AndreasGerken/demoPuppy/packs/puppy_v05_one_part/one_part_body.stl

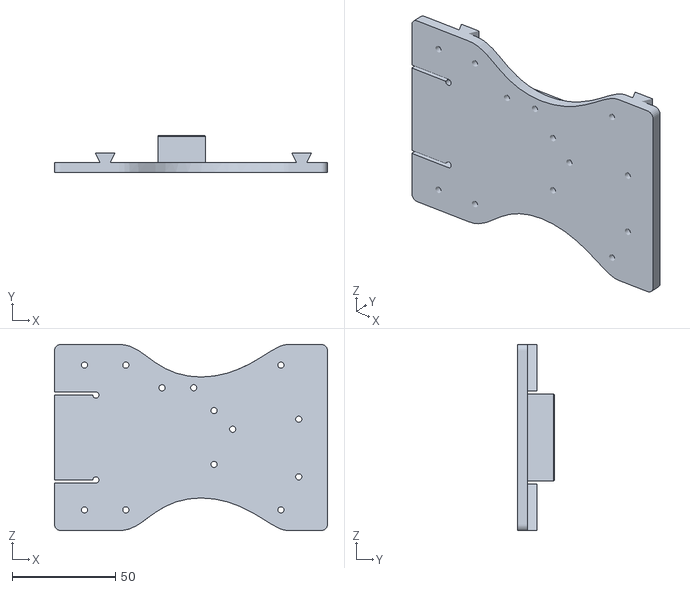
[picture p22: CAD file, 2017-08-01]
packs/puppy_v05_one_part/one_part_body.stl
132.0 x 18.0 x 90.0
