AndreasGerken/demoPuppy/models/servo_holder_HS-81/utility/HS-81MG_horn.SLDPRT

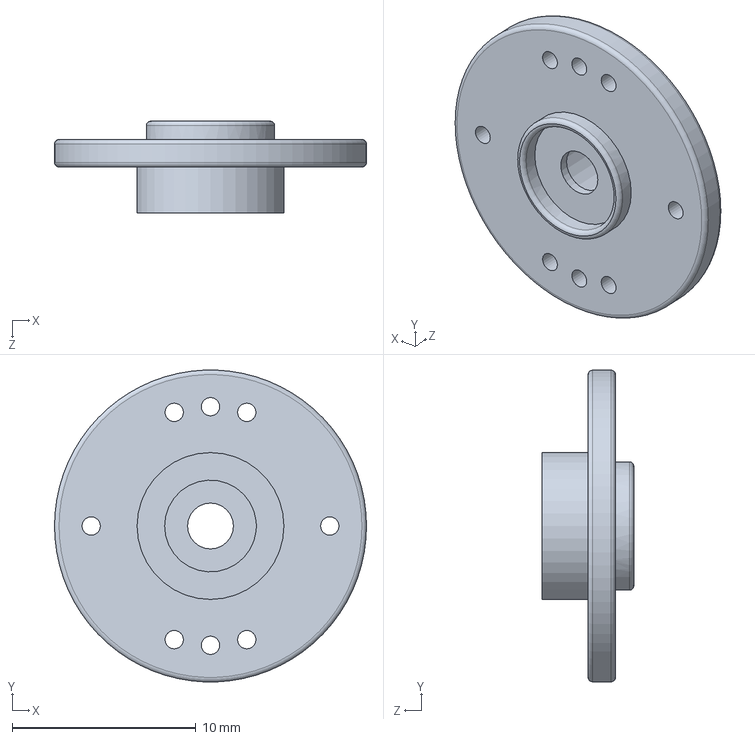
[picture p23: CAD file, 2017-07-04]
models/servo_holder_HS-81/utility/HS-81MG_horn.SLDPRT
17.0 x 17.0 x 5.00 mm
