AndreasGerken/demoPuppy/models/two_part_body/solidworks/holder_part.SLDPRT

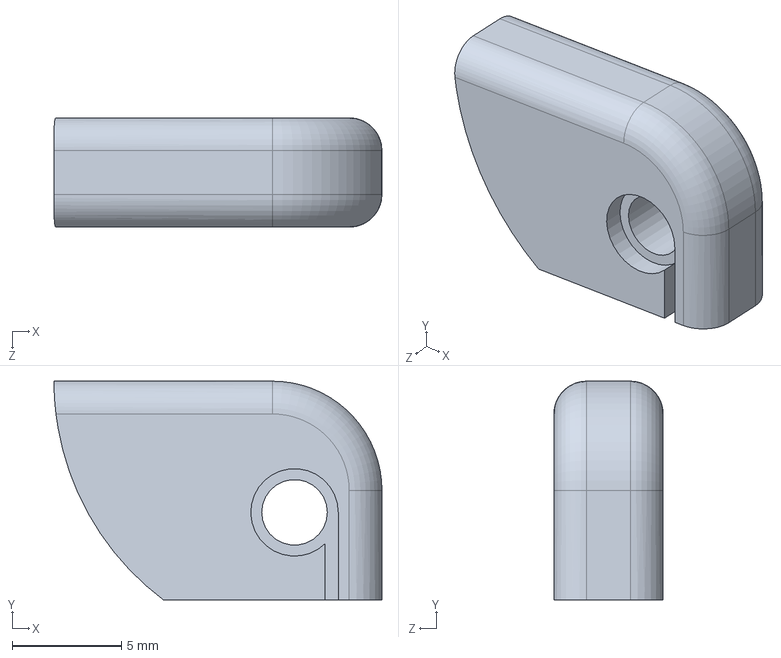
[picture p24: CAD file, 2017-07-04]
models/two_part_body/solidworks/holder_part.SLDPRT
15.0 x 10.0 x 5.00 mm
