AndreasGerken/demoPuppy/models/two_part_body/stl/puppy_v04_flexSpine - holder_part-1.STL

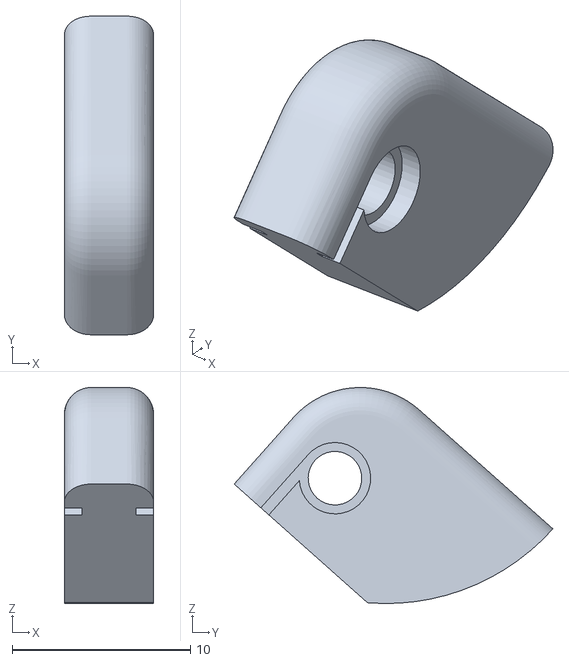
[picture p25: CAD file, 2017-07-04]
models/two_part_body/stl/puppy_v04_flexSpine - holder_part-1.STL
5.00 x 17.9 x 12.1
