AndreasGerken/demoPuppy/models/two_part_leg/solidworks/LowerLeg_v2_right.SLDPRT

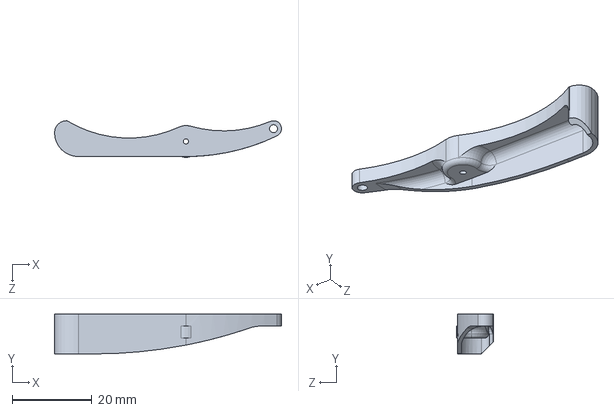
[picture p26: CAD file, 2017-07-04]
models/two_part_leg/solidworks/LowerLeg_v2_right.SLDPRT
57.0 x 10.0 x 9.18 mm
