AndreasGerken/demoPuppy/packs/puppy_v05_one_part/imu_MPU6050_holder.stl

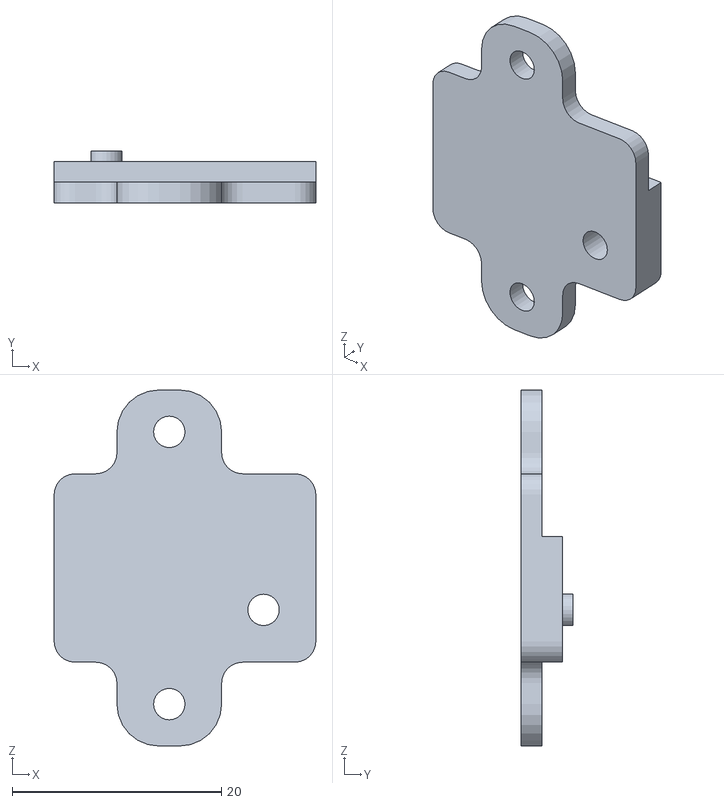
[picture p27: CAD file, 2017-07-04]
packs/puppy_v05_one_part/imu_MPU6050_holder.stl
25.0 x 5.00 x 34.0
