AndreasGerken/demoPuppy/models/two_part_body/solidworks/spine.SLDPRT

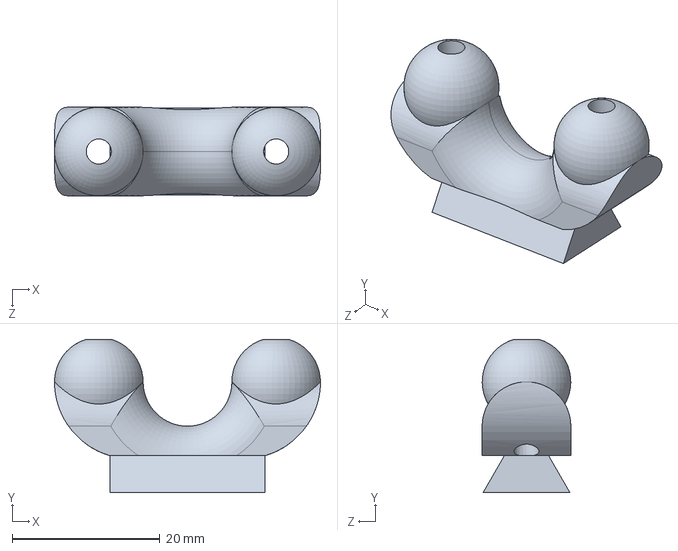
[picture p28: CAD file, 2017-07-04]
models/two_part_body/solidworks/spine.SLDPRT
36.0 x 20.8 x 12.0 mm
