AndreasGerken/demoPuppy/packs/puppy_v05_one_part/servo_holder_CS-3.stl

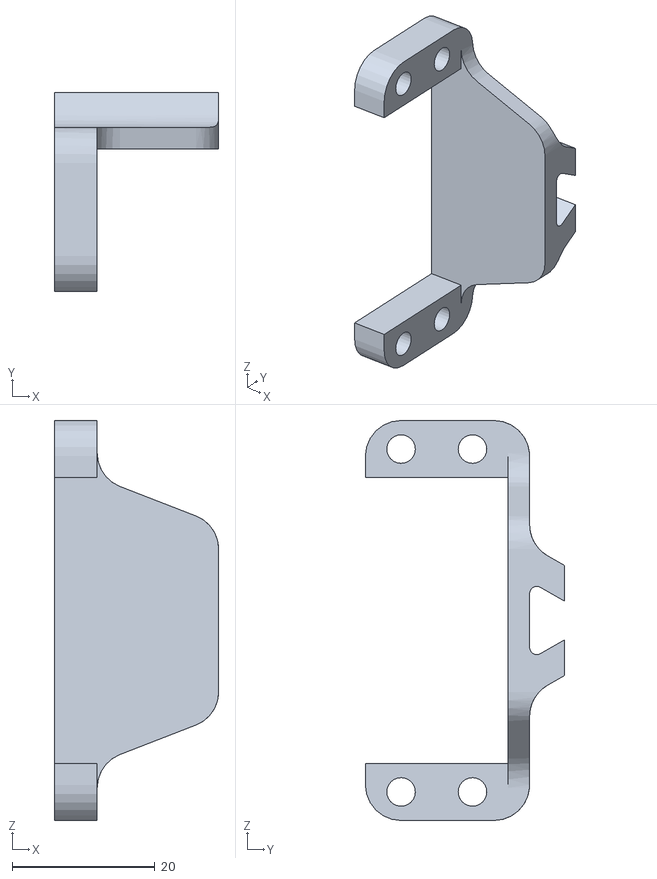
[picture p29: CAD file, 2017-07-04]
packs/puppy_v05_one_part/servo_holder_CS-3.stl
23.0 x 27.9 x 56.0
