AndreasGerken/demoPuppy/models/two_part_body/stl/puppy_v04_flexSpine - body_front-1.STL

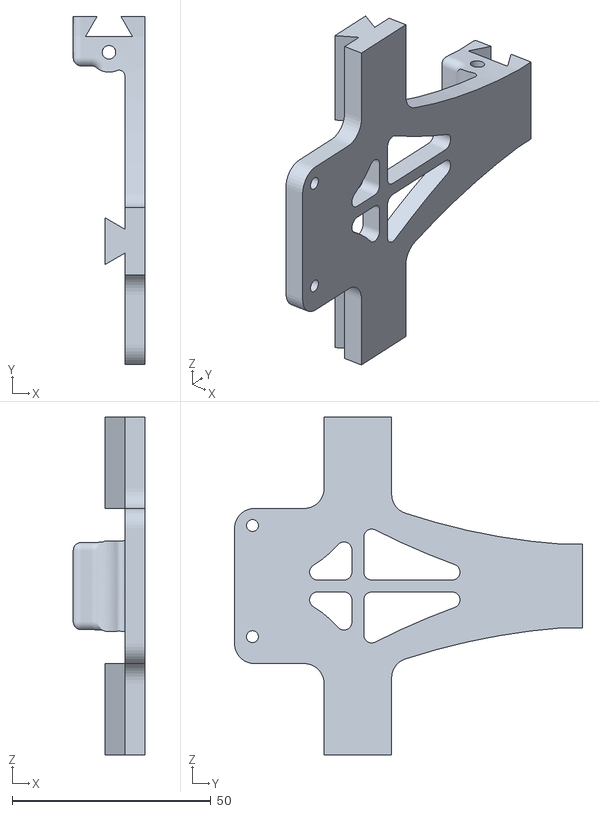
[picture p30: CAD file, 2017-07-04]
models/two_part_body/stl/puppy_v04_flexSpine - body_front-1.STL
18.0 x 87.5 x 85.0
