AndreasGerken/demoPuppy/models/two_part_leg/solidworks/UpperLeg_v2_right.SLDPRT

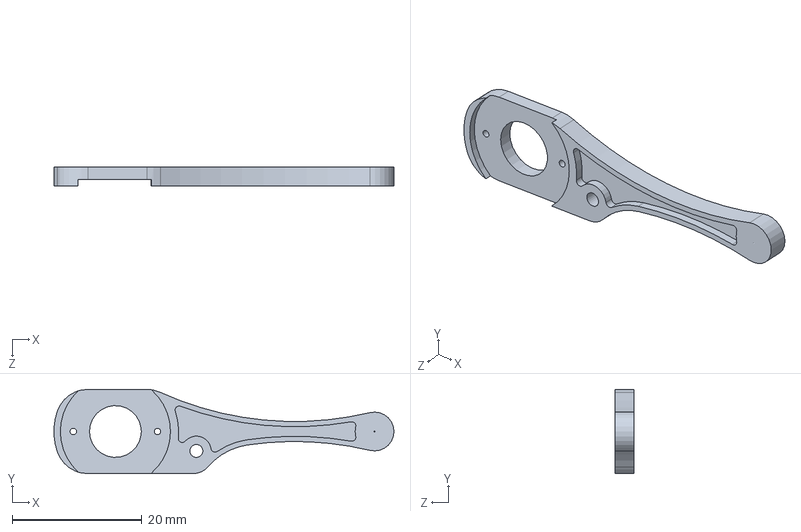
[picture p31: CAD file, 2017-07-04]
models/two_part_leg/solidworks/UpperLeg_v2_right.SLDPRT
52.5 x 13.0 x 3.00 mm
