AndreasGerken/demoPuppy/models/two_part_body/stl/puppy_v04_rigidSpine - rigid_spine-1.STL

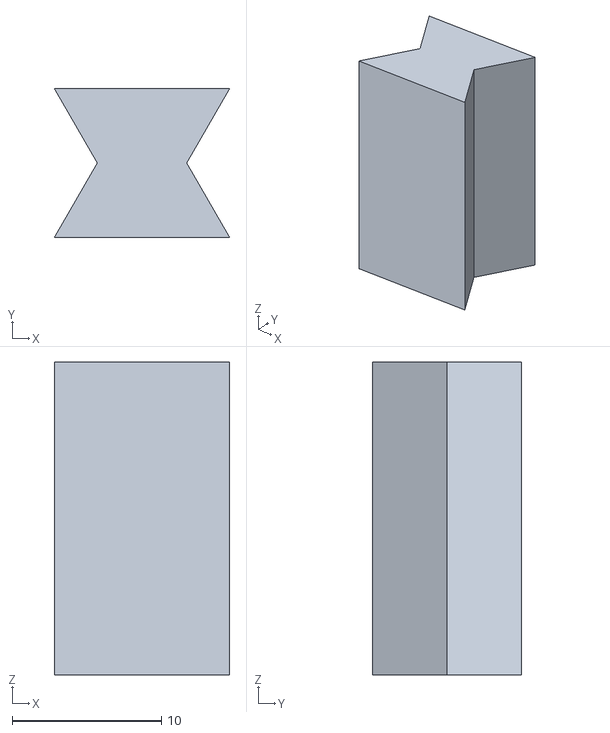
[picture p32: CAD file, 2017-07-04]
models/two_part_body/stl/puppy_v04_rigidSpine - rigid_spine-1.STL
11.8 x 10.0 x 21.0
