AndreasGerken/demoPuppy/models/two_part_body/stl/puppy_v04_flexSpine - holder_top-1.STL

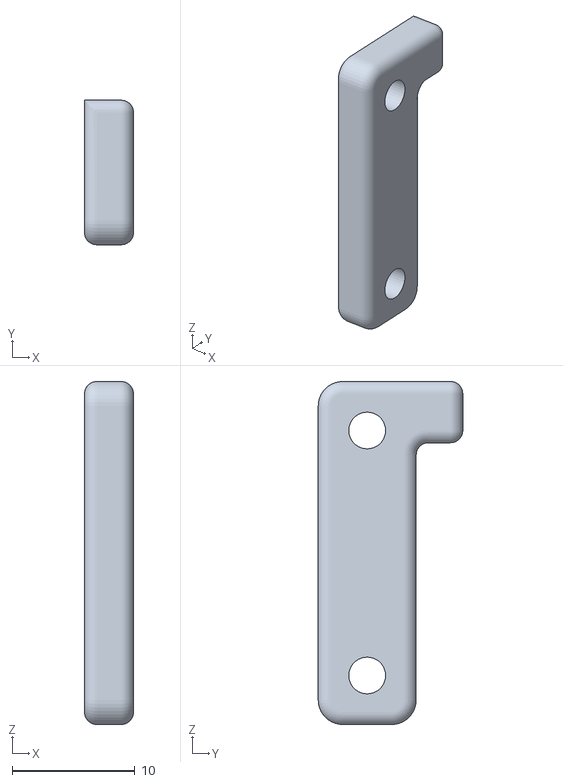
[picture p33: CAD file, 2017-07-04]
models/two_part_body/stl/puppy_v04_flexSpine - holder_top-1.STL
4.00 x 11.8 x 28.0
