AndreasGerken/demoPuppy/models/two_part_leg/solidworks/spacerM3_1mm.SLDPRT

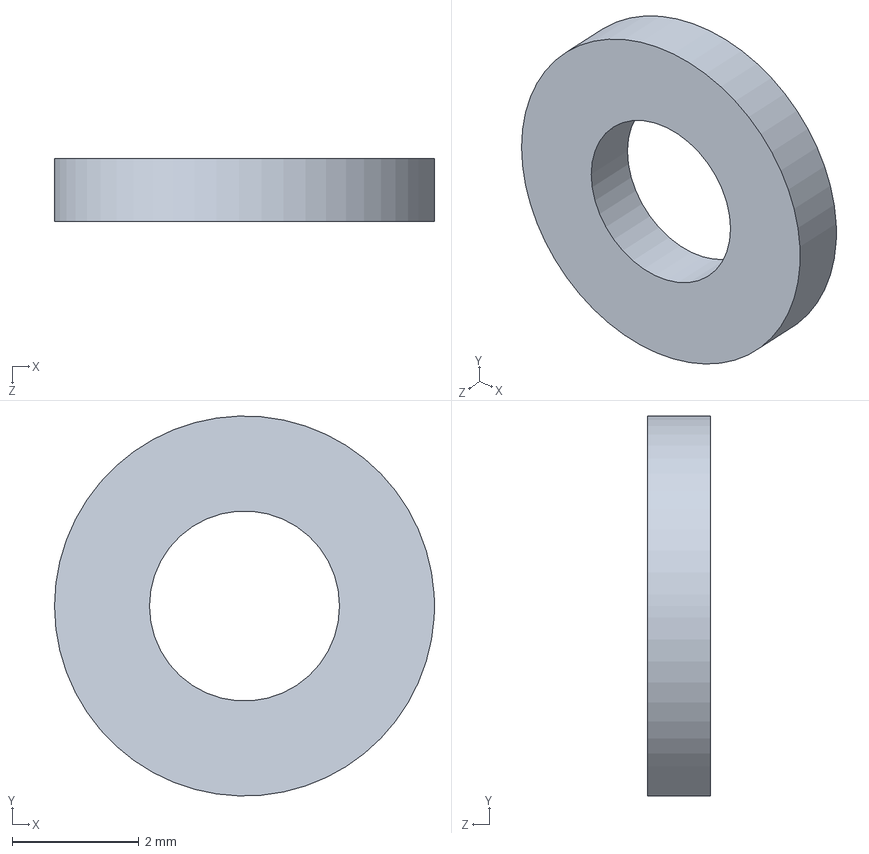
[picture p34: CAD file, 2017-07-04]
models/two_part_leg/solidworks/spacerM3_1mm.SLDPRT
6.00 x 6.00 x 1.00 mm
